JeremyTubongbanua/blind_person_assistant/stls/SmartCane/SmartCaneAssembly/Adapter.stl

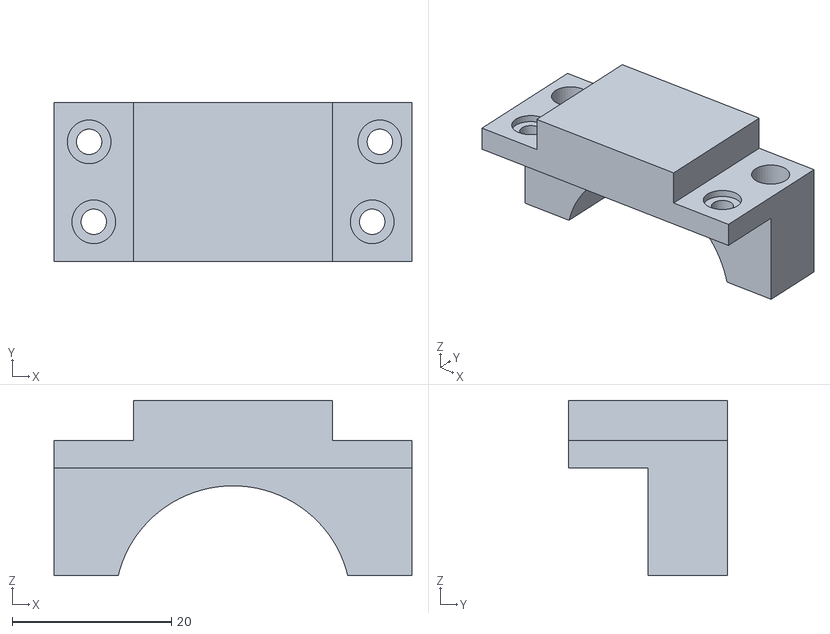
[picture p88: CAD file, 2025-04-05]
stls/SmartCane/SmartCaneAssembly/Adapter.stl
45.0 x 20.0 x 22.0
