JeremyTubongbanua/blind_person_assistant/stls/SystemGateway/PowerBankClamp.stl

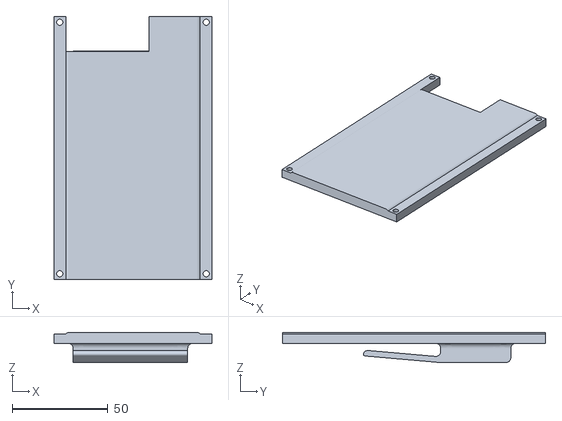
[picture p89: CAD file, 2025-04-05]
stls/SystemGateway/PowerBankClamp.stl
82.7 x 137.7 x 15.8
