JeremyTubongbanua/blind_person_assistant/stls/Headset/HeadsetFrame/Frame.stl

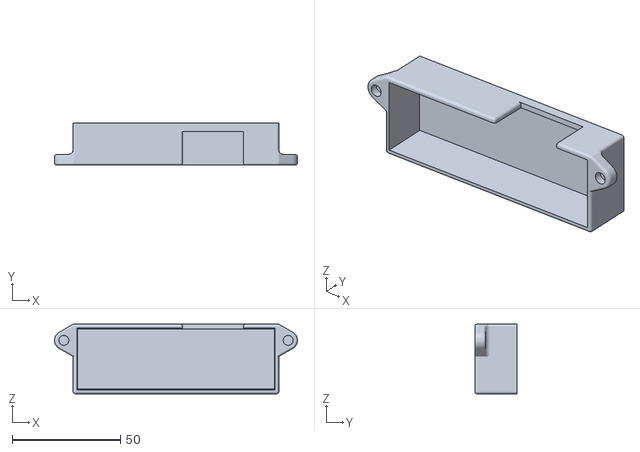
[picture p90: CAD file, 2025-04-05]
stls/Headset/HeadsetFrame/Frame.stl
112.0 x 19.5 x 32.1
