JeremyTubongbanua/blind_person_assistant/stls/Headset/LuxonisOakDLite.stl

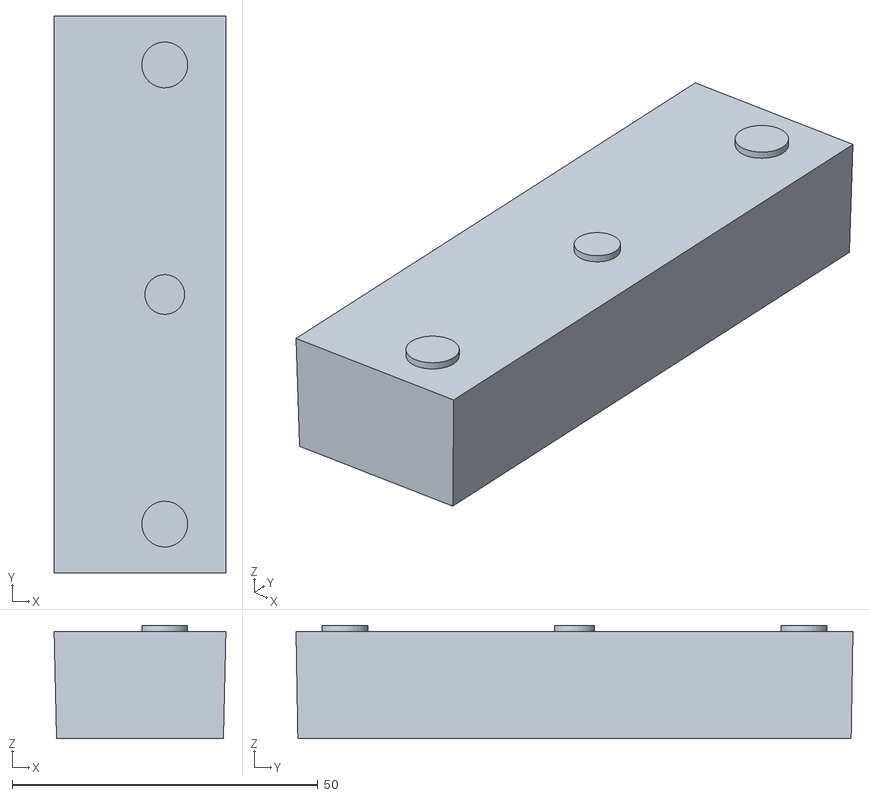
[picture p91: CAD file, 2025-04-05]
stls/Headset/LuxonisOakDLite.stl
28.1 x 91.1 x 18.5
