JeremyTubongbanua/blind_person_assistant/stls/SmartCane/ElectronicsHolder/WAGOHolder.stl

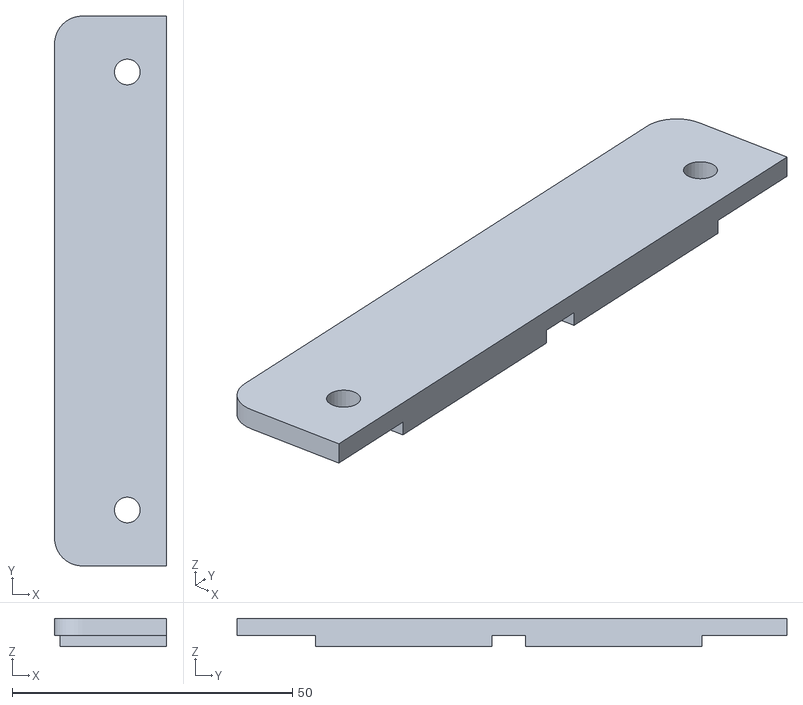
[picture p92: CAD file, 2025-04-05]
stls/SmartCane/ElectronicsHolder/WAGOHolder.stl
20.0 x 98.2 x 5.00
