JeremyTubongbanua/blind_person_assistant/stls/SystemGateway/RaspberryPi.stl

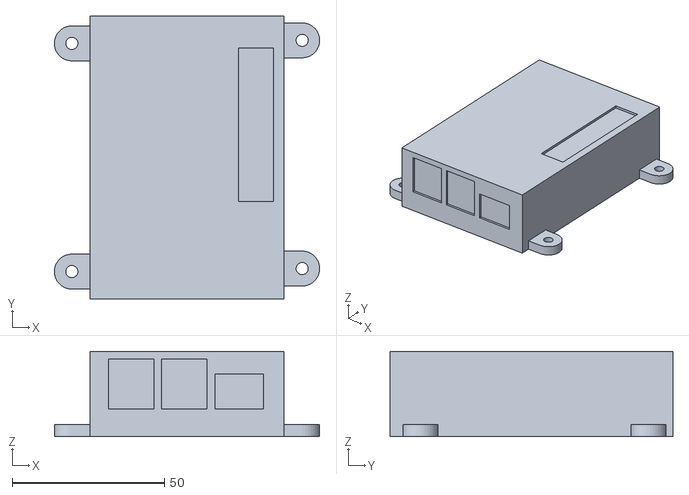
[picture p93: CAD file, 2025-04-05]
stls/SystemGateway/RaspberryPi.stl
87.2 x 93.0 x 28.0
