JeremyTubongbanua/blind_person_assistant/stls/Headset/HeadsetFrame/Arc.stl

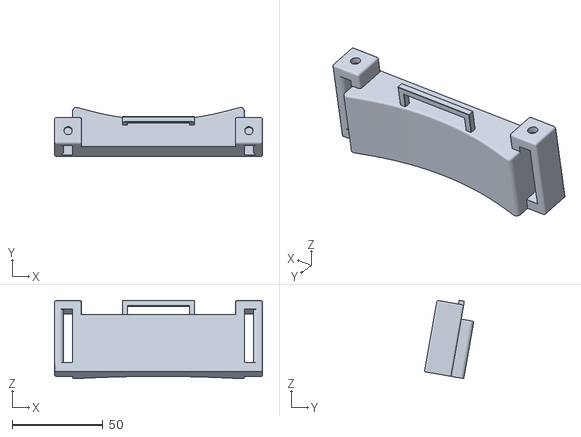
[picture p94: CAD file, 2025-04-05]
stls/Headset/HeadsetFrame/Arc.stl
114.8 x 27.2 x 43.2
