JeremyTubongbanua/blind_person_assistant/stls/Headset/USBSpeaker.stl

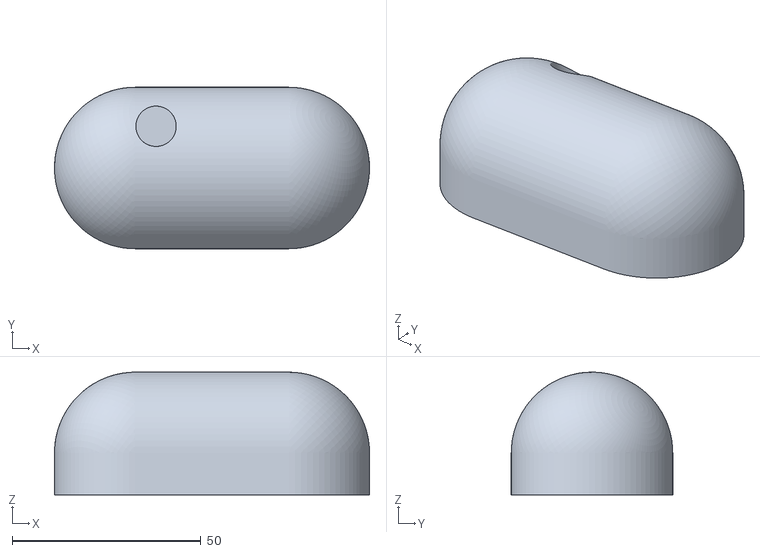
[picture p95: CAD file, 2025-04-05]
stls/Headset/USBSpeaker.stl
83.5 x 42.8 x 32.5
