JeremyTubongbanua/blind_person_assistant/stls/SmartCane/ElectronicsHolder/TopHolder.stl

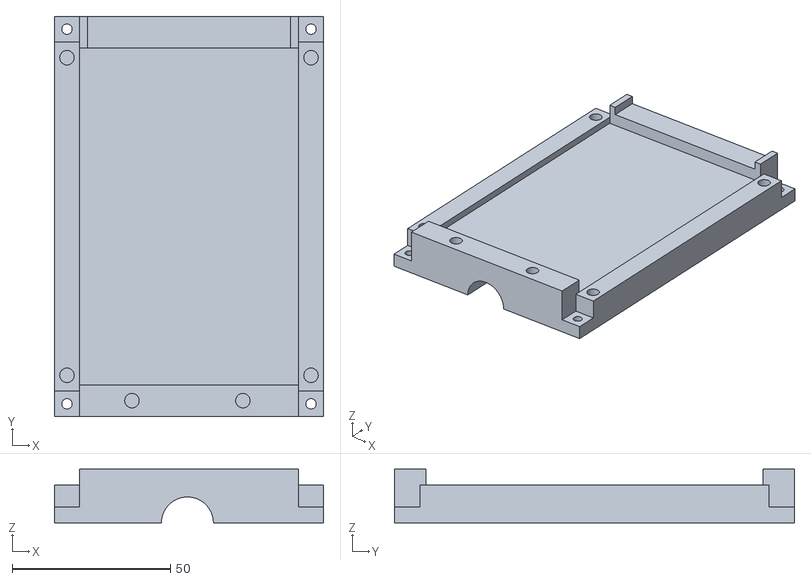
[picture p96: CAD file, 2025-04-05]
stls/SmartCane/ElectronicsHolder/TopHolder.stl
85.0 x 126.2 x 17.0
