JeremyTubongbanua/blind_person_assistant/stls/SystemGateway/RightMangoClamp.stl

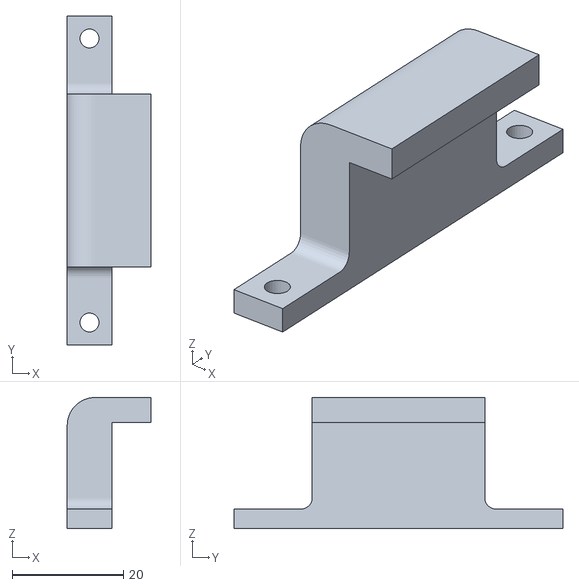
[picture p97: CAD file, 2025-04-05]
stls/SystemGateway/RightMangoClamp.stl
15.0 x 59.0 x 23.5
