JeremyTubongbanua/blind_person_assistant/stls/Headset/Lip.stl

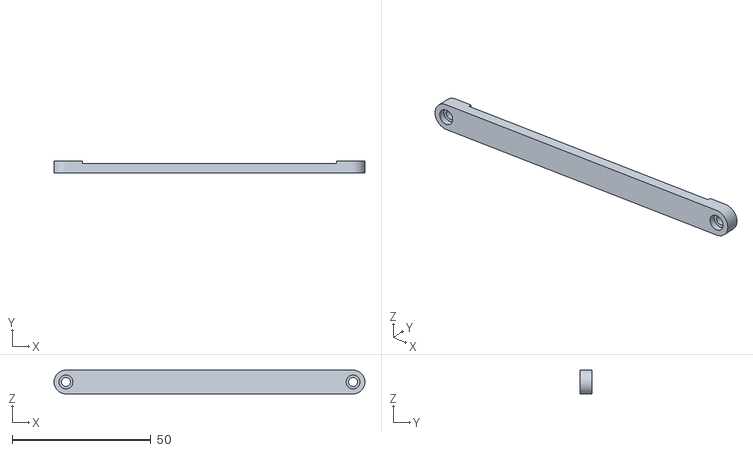
[picture p98: CAD file, 2025-04-05]
stls/Headset/Lip.stl
112.0 x 4.50 x 8.60
