JeremyTubongbanua/blind_person_assistant/stls/SmartCane/ButtonInterface/Button.stl

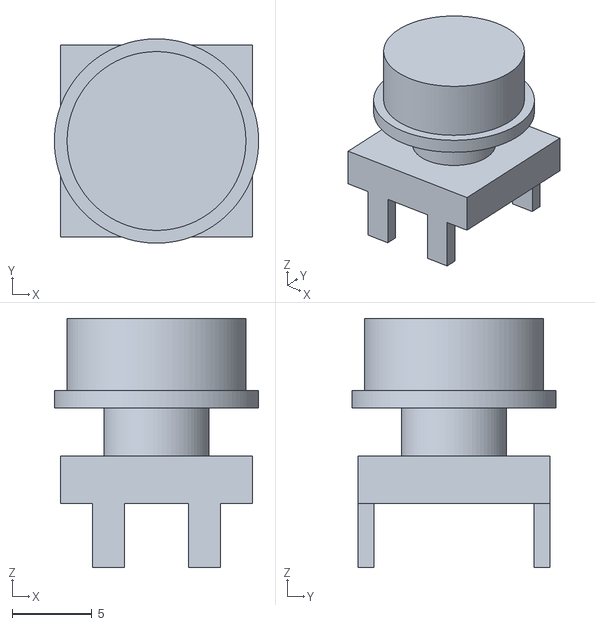
[picture p99: CAD file, 2025-04-05]
stls/SmartCane/ButtonInterface/Button.stl
12.8 x 12.8 x 15.6
