JeremyTubongbanua/blind_person_assistant/stls/Headset/SpeakerCage.stl

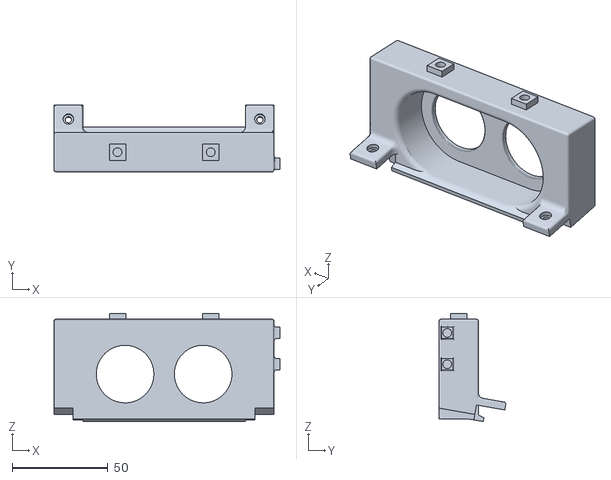
[picture p100: CAD file, 2025-04-05]
stls/Headset/SpeakerCage.stl
117.8 x 34.8 x 56.4
