JeremyTubongbanua/blind_person_assistant/stls/SmartCane/ButtonInterface/VibrationMotor.stl

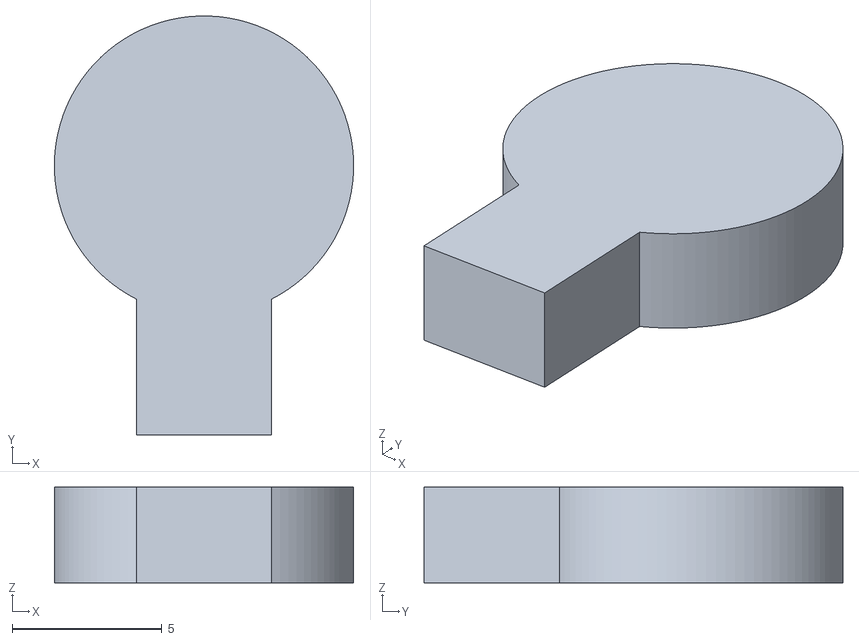
[picture p101: CAD file, 2025-04-05]
stls/SmartCane/ButtonInterface/VibrationMotor.stl
10.00 x 14.0 x 3.20
