JeremyTubongbanua/blind_person_assistant/stls/SmartCane/ElectronicsHolder/Relay.stl

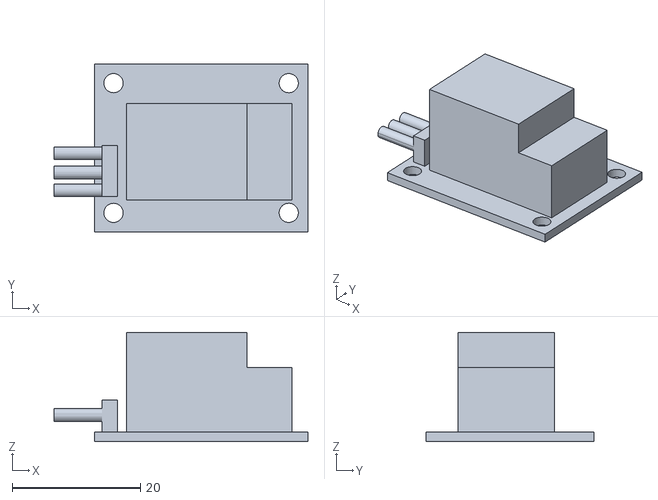
[picture p102: CAD file, 2025-04-05]
stls/SmartCane/ElectronicsHolder/Relay.stl
39.6 x 26.2 x 17.0
