JeremyTubongbanua/blind_person_assistant/stls/SystemGateway/PowerBank.stl

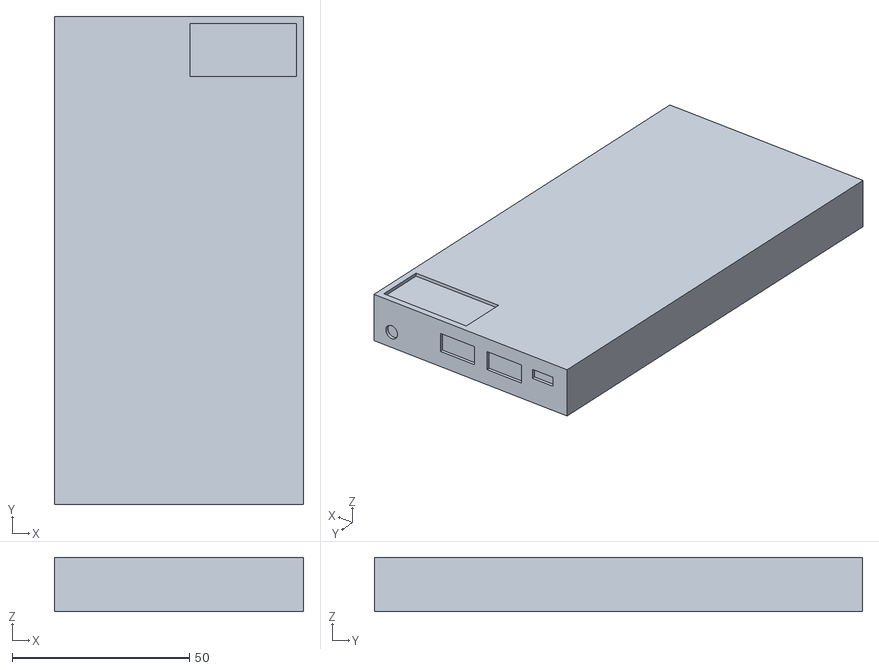
[picture p103: CAD file, 2025-04-05]
stls/SystemGateway/PowerBank.stl
70.2 x 137.7 x 15.3
