JeremyTubongbanua/blind_person_assistant/stls/Headset/SpeakerClamp.stl

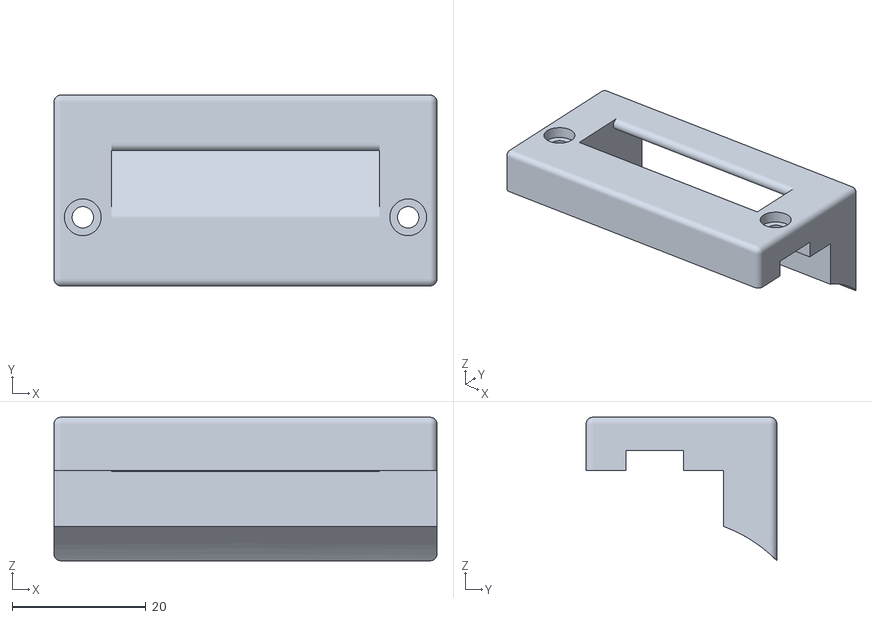
[picture p104: CAD file, 2025-04-05]
stls/Headset/SpeakerClamp.stl
57.2 x 28.5 x 21.5
