JeremyTubongbanua/blind_person_assistant/stls/SmartCane/ButtonInterface/Base.stl

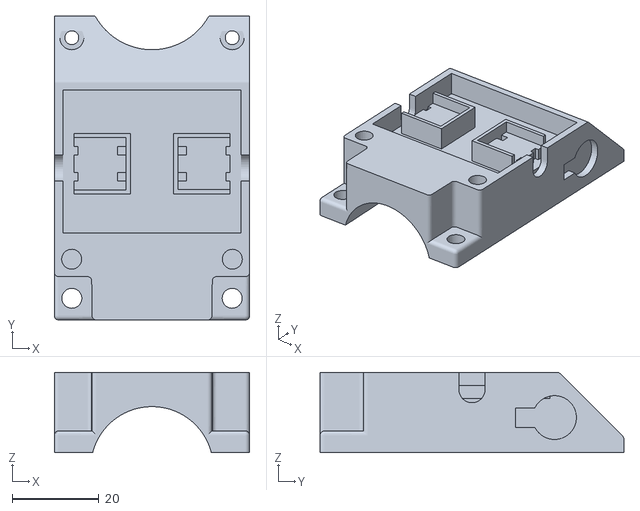
[picture p105: CAD file, 2025-04-05]
stls/SmartCane/ButtonInterface/Base.stl
45.0 x 70.0 x 18.5
