JeremyTubongbanua/blind_person_assistant/stls/SystemGateway/PowerBankEnclosure.stl

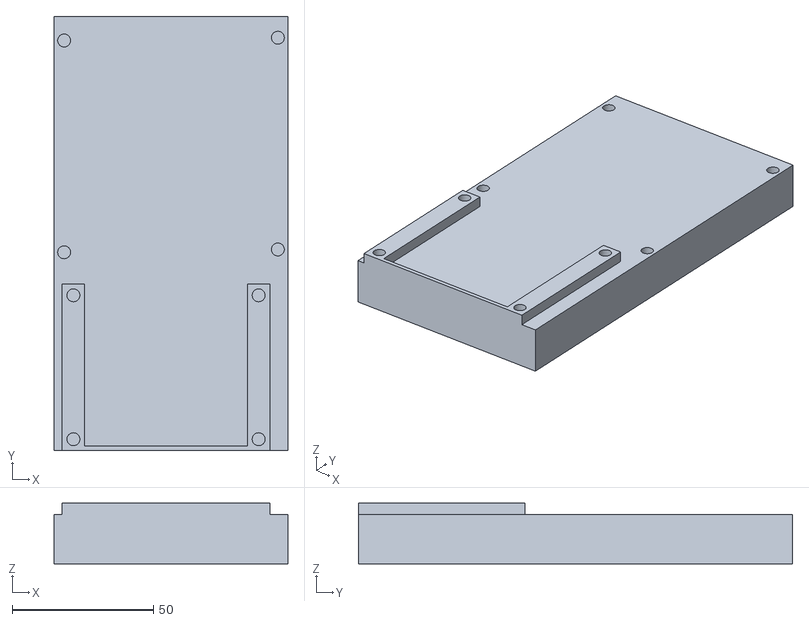
[picture p106: CAD file, 2025-04-05]
stls/SystemGateway/PowerBankEnclosure.stl
82.7 x 153.7 x 21.5
