JeremyTubongbanua/blind_person_assistant/stls/SmartCane/ButtonInterface/TopLayer.stl

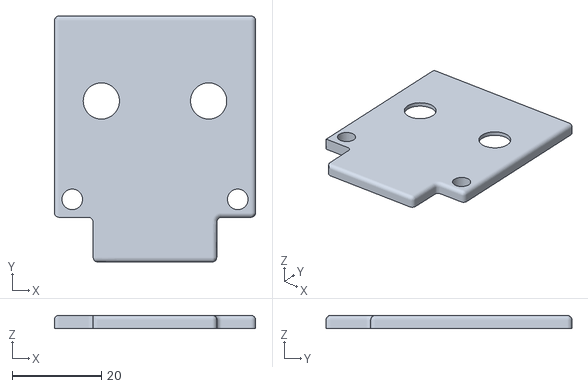
[picture p107: CAD file, 2025-04-05]
stls/SmartCane/ButtonInterface/TopLayer.stl
45.0 x 55.0 x 2.95
