JeremyTubongbanua/blind_person_assistant/stls/SmartCane/ElectronicsHolder/CaneStem.stl

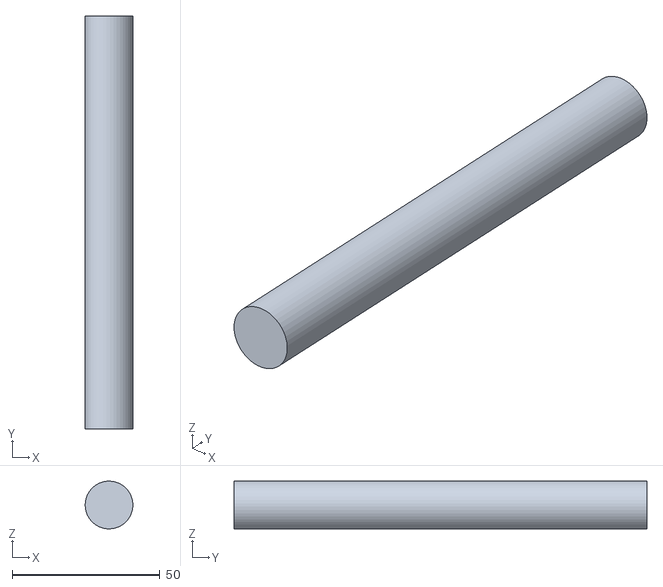
[picture p108: CAD file, 2025-04-05]
stls/SmartCane/ElectronicsHolder/CaneStem.stl
16.2 x 140.0 x 16.2
