JeremyTubongbanua/blind_person_assistant/stls/SmartCane/ElectronicsHolder/PowerBank.stl

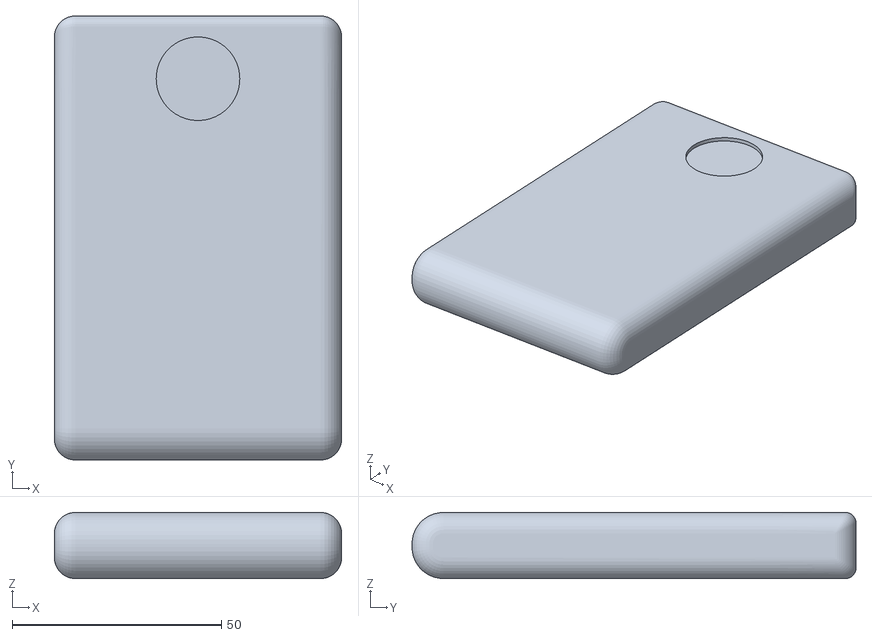
[picture p109: CAD file, 2025-04-05]
stls/SmartCane/ElectronicsHolder/PowerBank.stl
68.7 x 106.2 x 15.8
